winSC1ENCE/rancillio-mini/docs/img/trockenaufbau.png

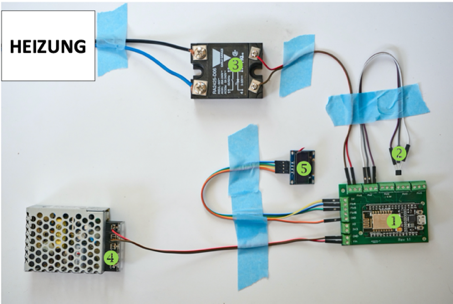
docs/img/trockenaufbau.png
