winSC1ENCE/rancillio-mini/docs/img/OnlyPIDRancilio.png

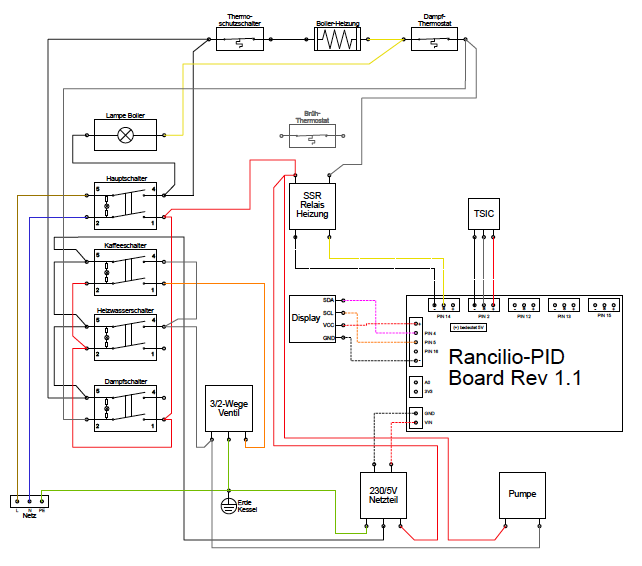
docs/img/OnlyPIDRancilio.png
