winSC1ENCE/rancillio-mini/docs/img/OrginalSchaltplanRancilio.png

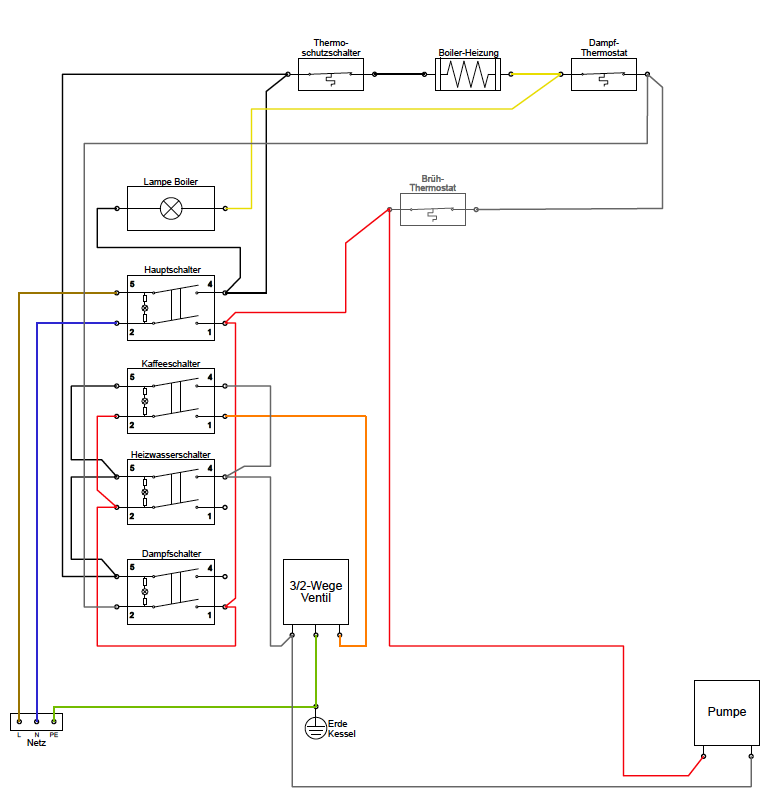
docs/img/OrginalSchaltplanRancilio.png
