winSC1ENCE/rancillio-mini/docs/img/platine_rev1.2.png

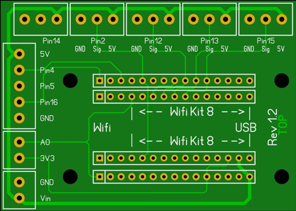
docs/img/platine_rev1.2.png
