winSC1ENCE/rancillio-mini/docs/img/relais_1.jpg

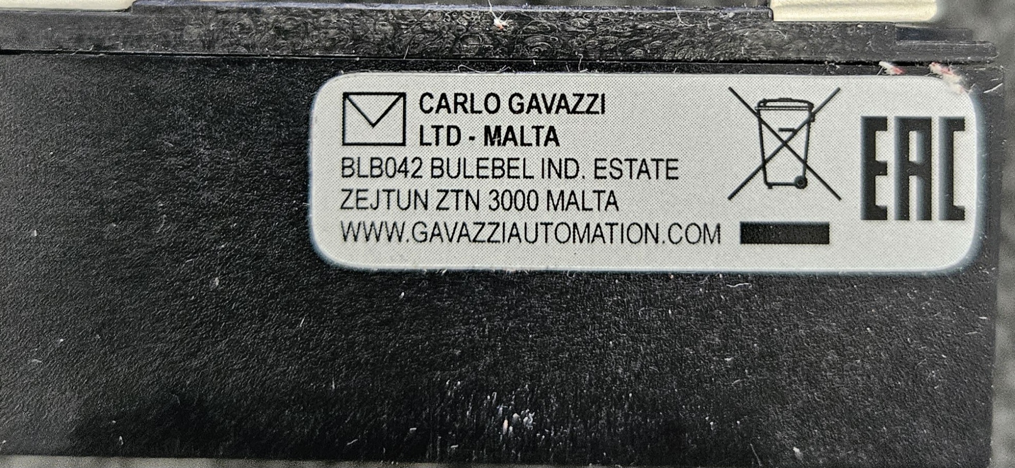
docs/img/relais_1.jpg
