winSC1ENCE/rancillio-mini/docs/img/relais_datasheet_1.jpg

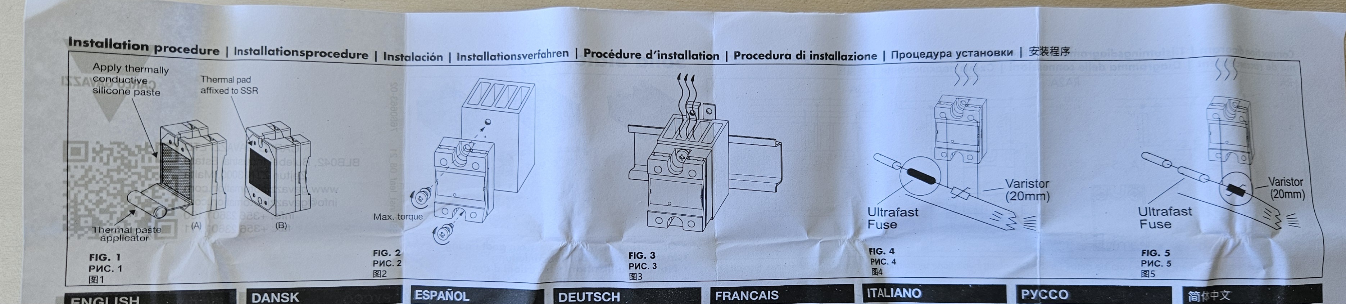
docs/img/relais_datasheet_1.jpg
