winSC1ENCE/rancillio-mini/docs/img/relais_datasheet_2.jpg

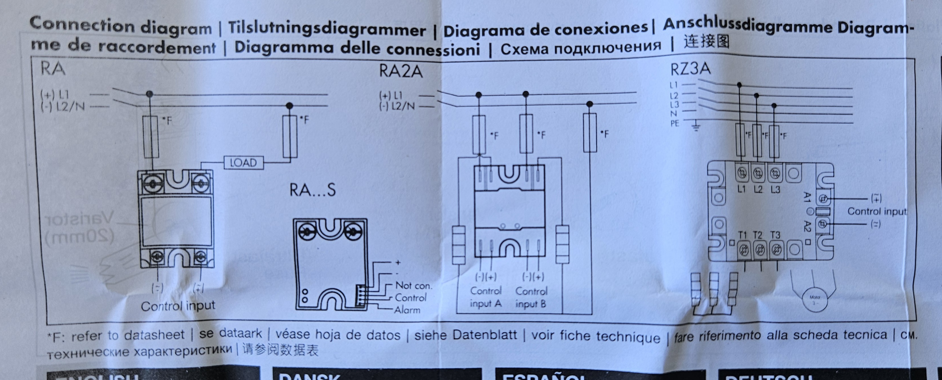
docs/img/relais_datasheet_2.jpg
