winSC1ENCE/rancillio-mini/docs/img/relais_datasheet_3.jpg

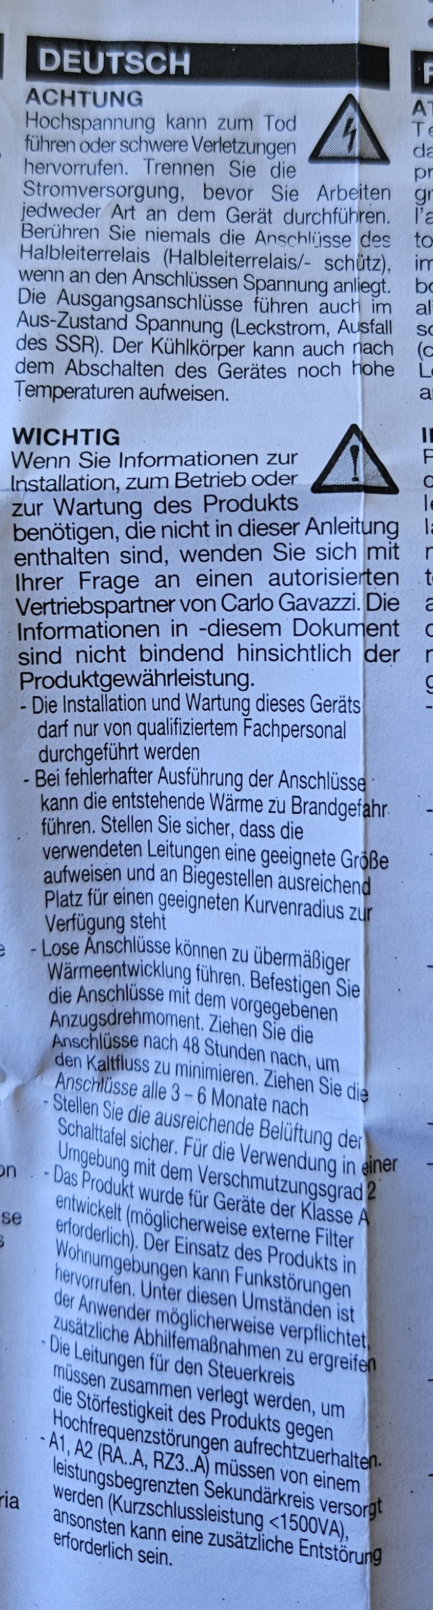
docs/img/relais_datasheet_3.jpg
