winSC1ENCE/rancillio-mini/docs/img/temp_sensor_belegung.jpg

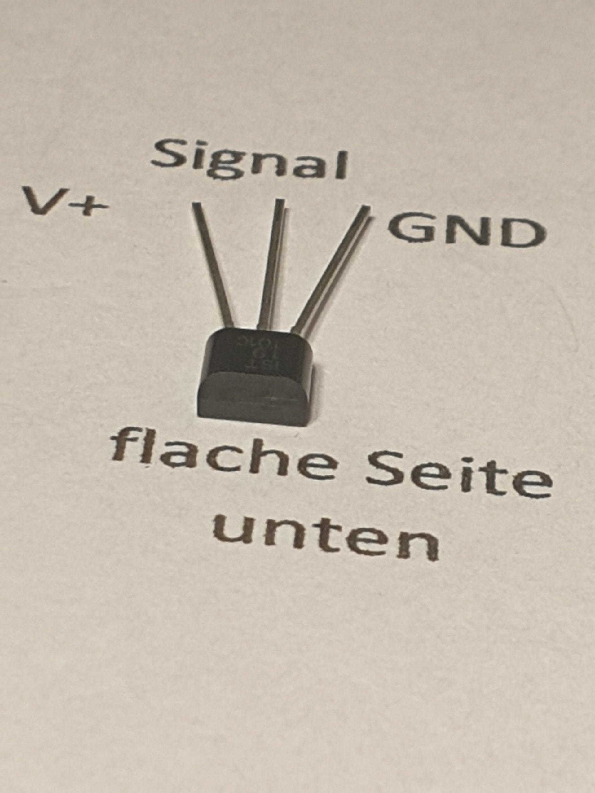
docs/img/temp_sensor_belegung.jpg
