winSC1ENCE/rancillio-mini/img/IMG_0040.jpeg

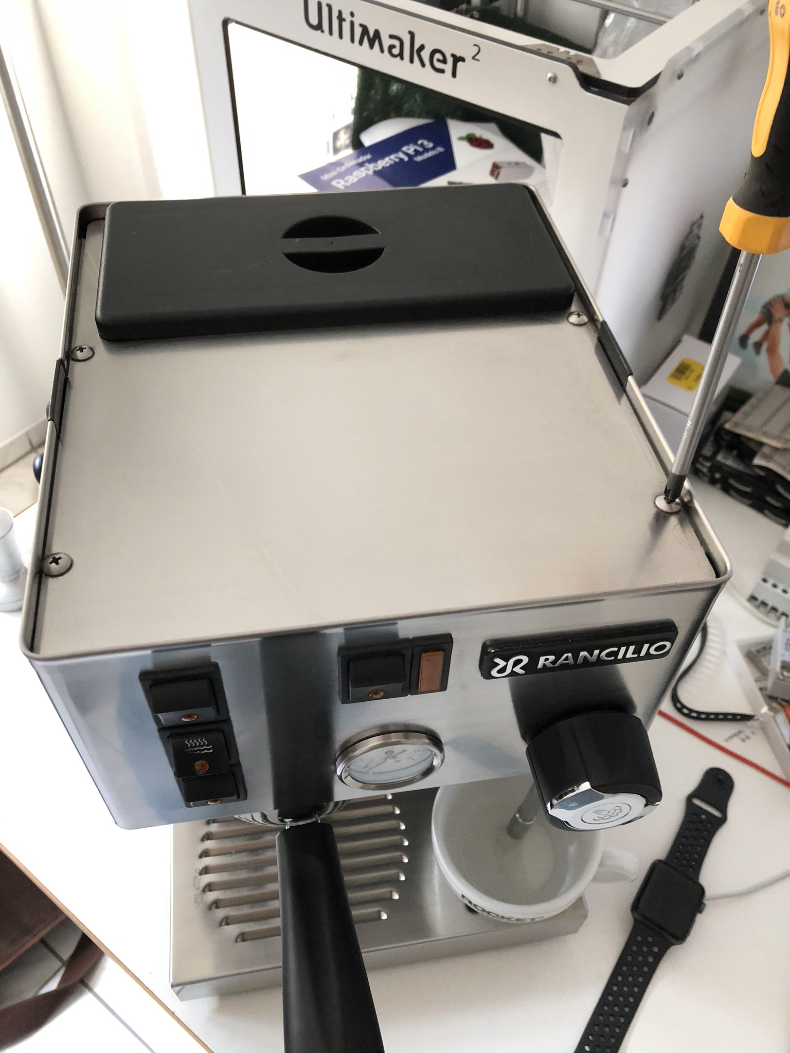
img/IMG_0040.jpeg
