winSC1ENCE/rancillio-mini/img/IMG_0041.jpeg

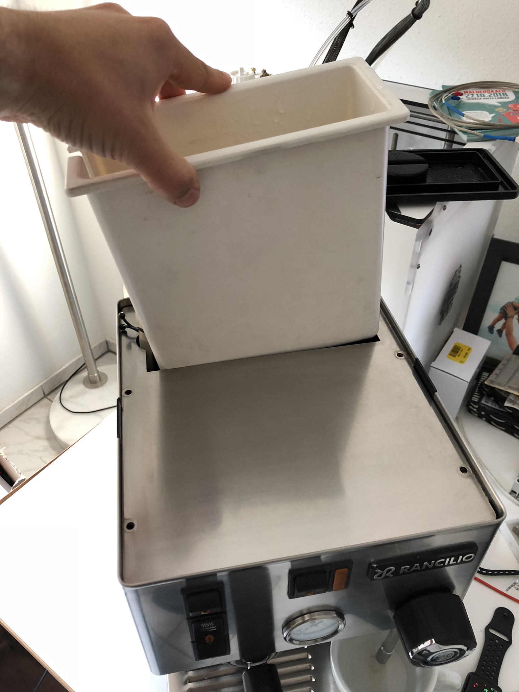
img/IMG_0041.jpeg
