winSC1ENCE/rancillio-mini/img/IMG_0042.jpeg

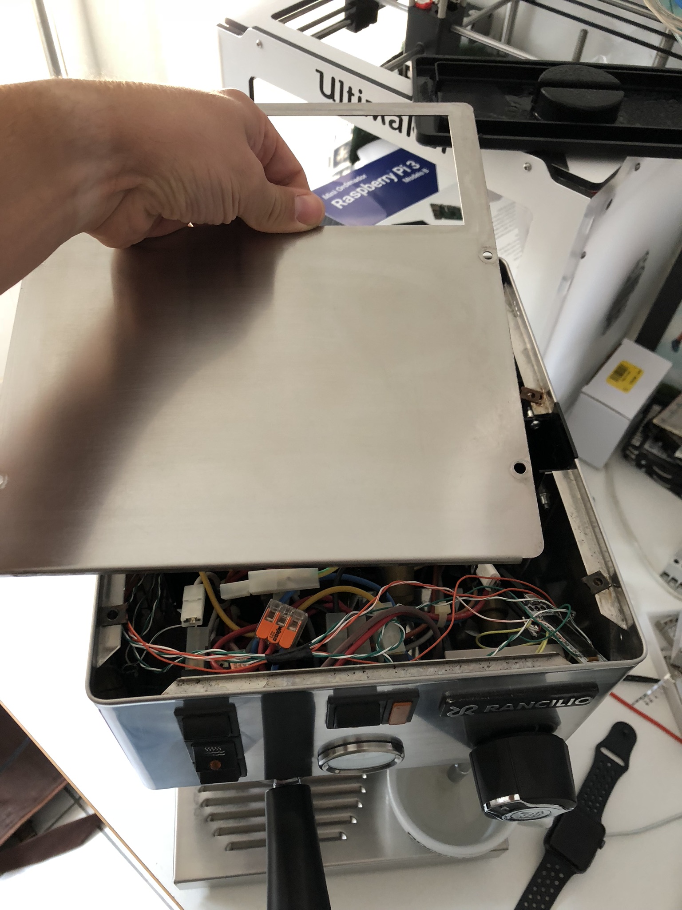
img/IMG_0042.jpeg
