winSC1ENCE/rancillio-mini/img/IMG_0043.jpeg

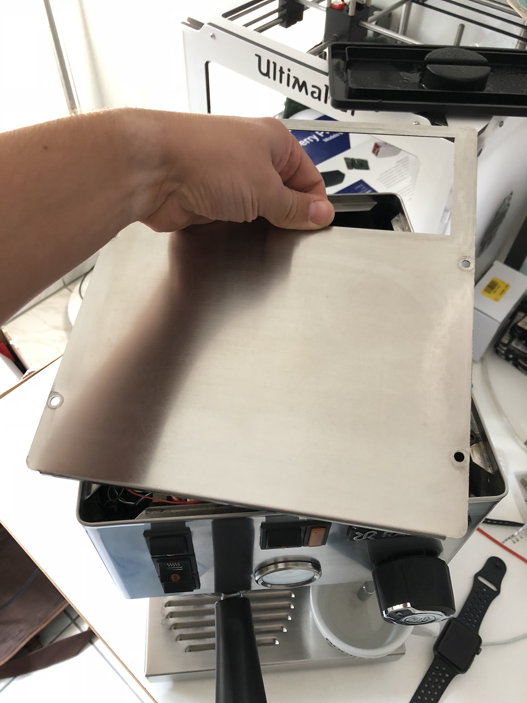
img/IMG_0043.jpeg
