winSC1ENCE/rancillio-mini/img/IMG_0044.jpeg

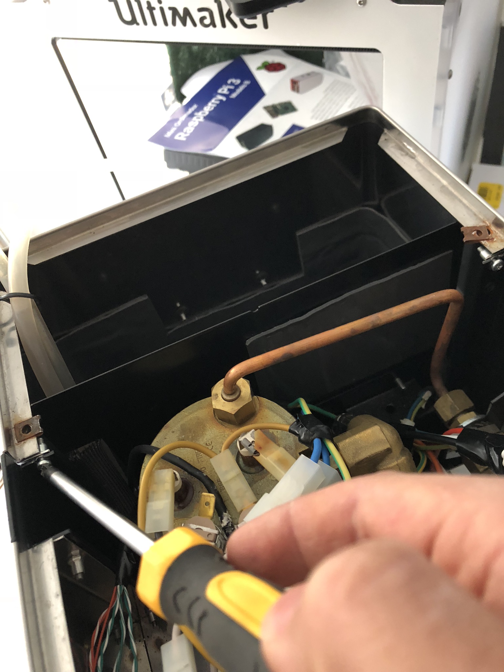
img/IMG_0044.jpeg
