winSC1ENCE/rancillio-mini/img/IMG_0045.jpeg

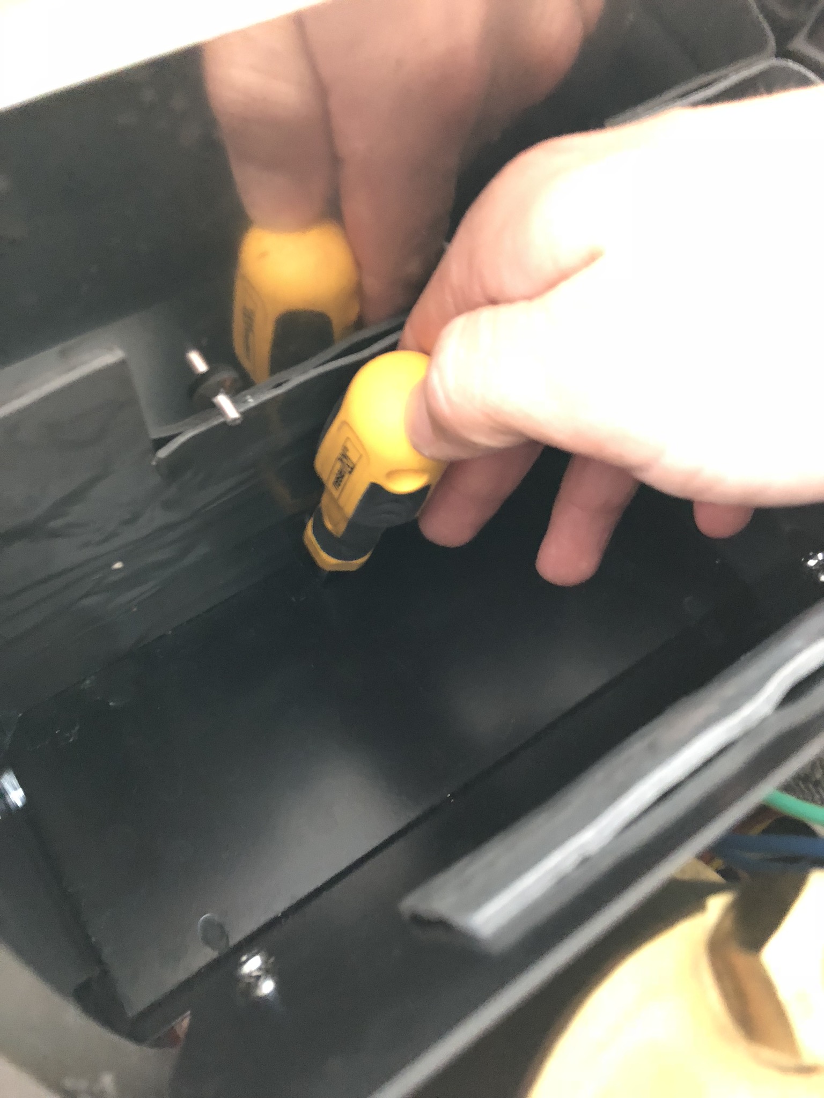
img/IMG_0045.jpeg
