winSC1ENCE/rancillio-mini/img/IMG_0046.jpeg

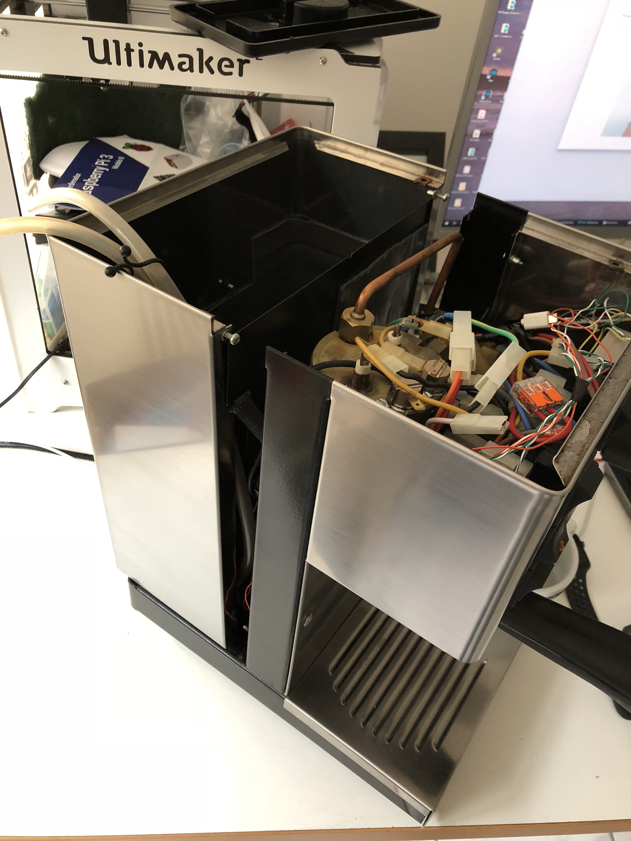
img/IMG_0046.jpeg
