winSC1ENCE/rancillio-mini/img/IMG_0047.jpeg

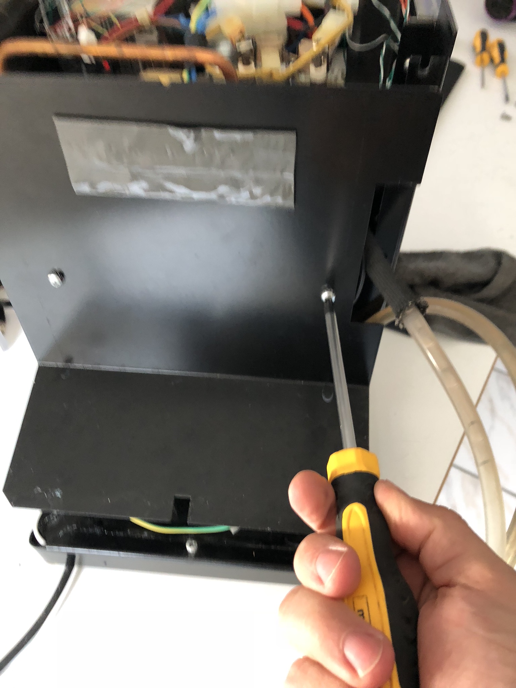
img/IMG_0047.jpeg
