winSC1ENCE/rancillio-mini/img/IMG_0048.jpeg

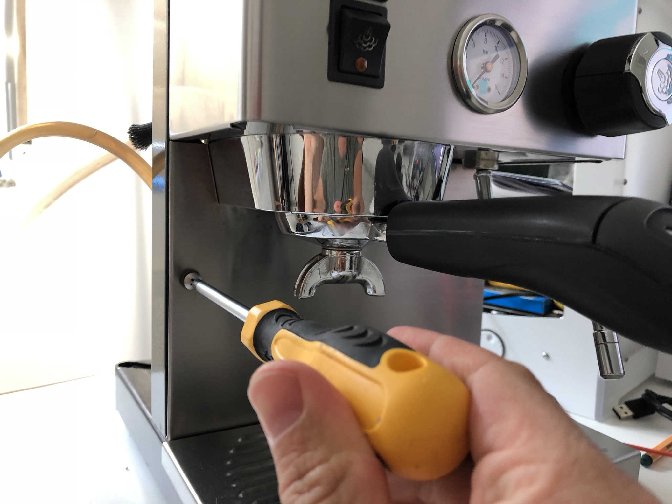
img/IMG_0048.jpeg
