winSC1ENCE/rancillio-mini/img/IMG_0049.jpeg

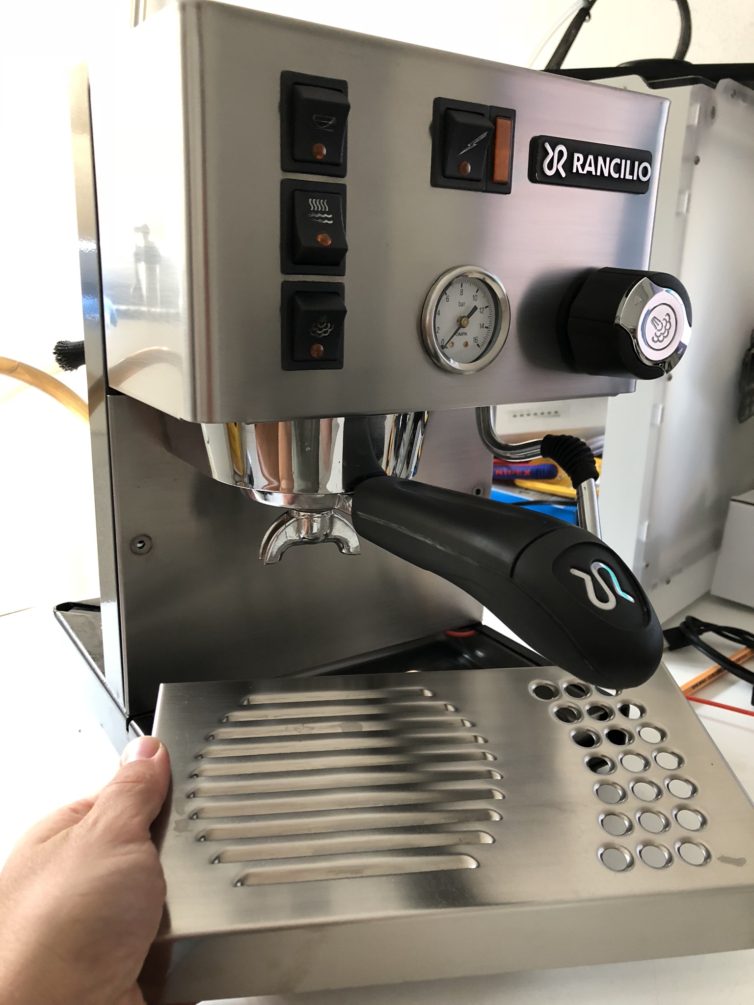
img/IMG_0049.jpeg
