winSC1ENCE/rancillio-mini/img/IMG_0050.jpeg

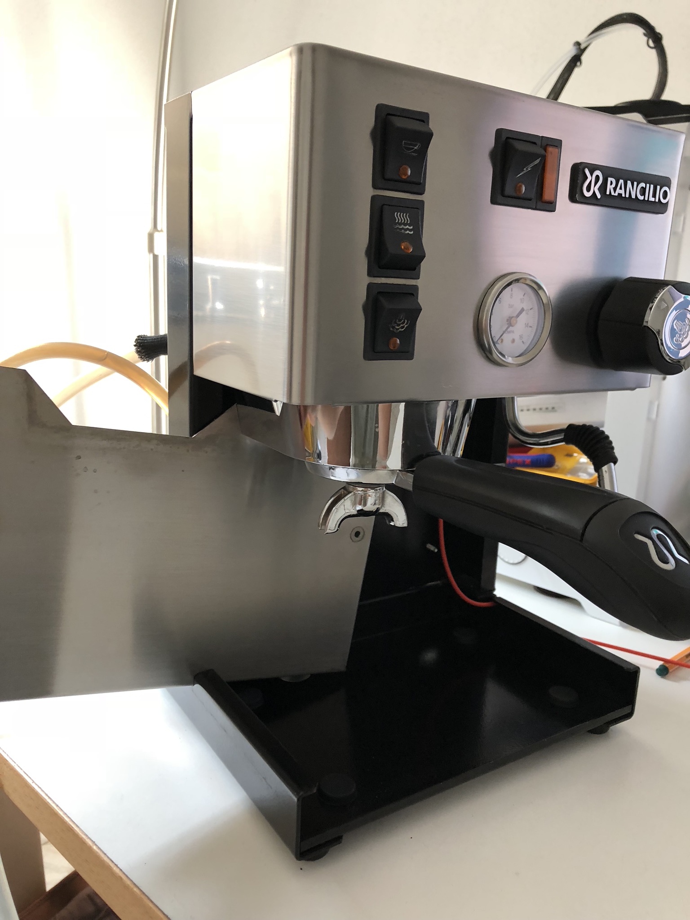
img/IMG_0050.jpeg
