winSC1ENCE/rancillio-mini/img/IMG_0076.jpeg

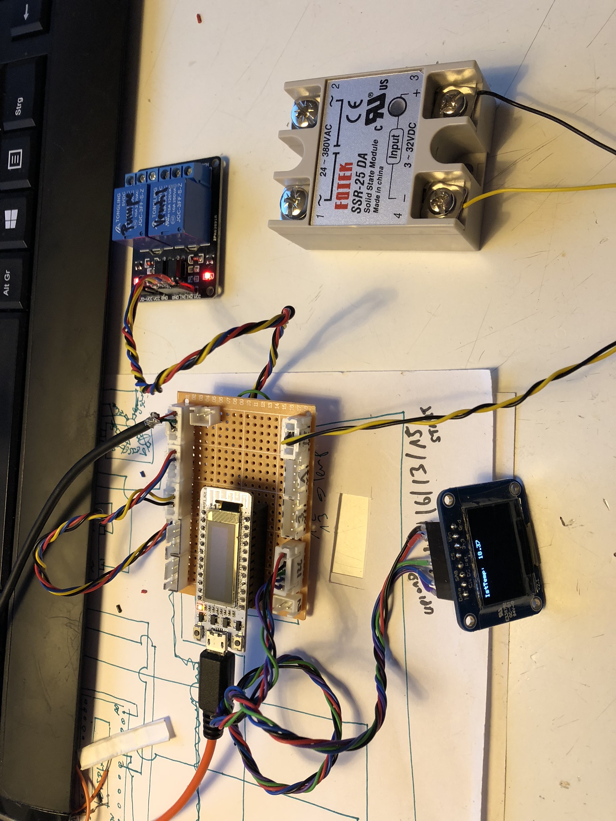
img/IMG_0076.jpeg
