winSC1ENCE/rancillio-mini/img/IMG_0078.jpeg

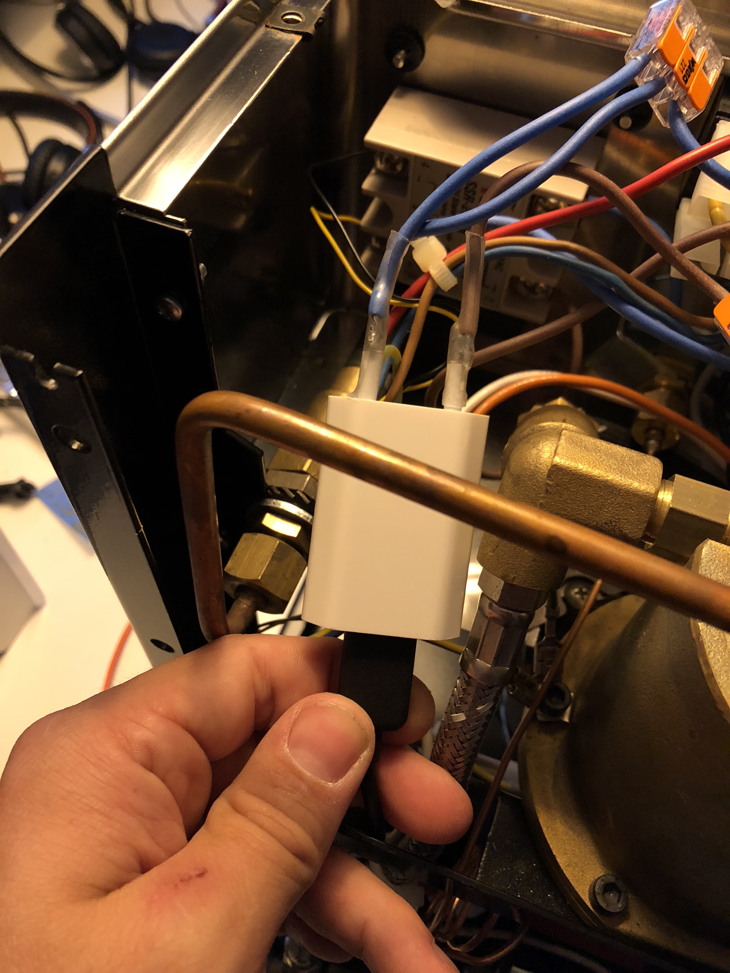
img/IMG_0078.jpeg
