winSC1ENCE/rancillio-mini/img/IMG_0079.jpeg

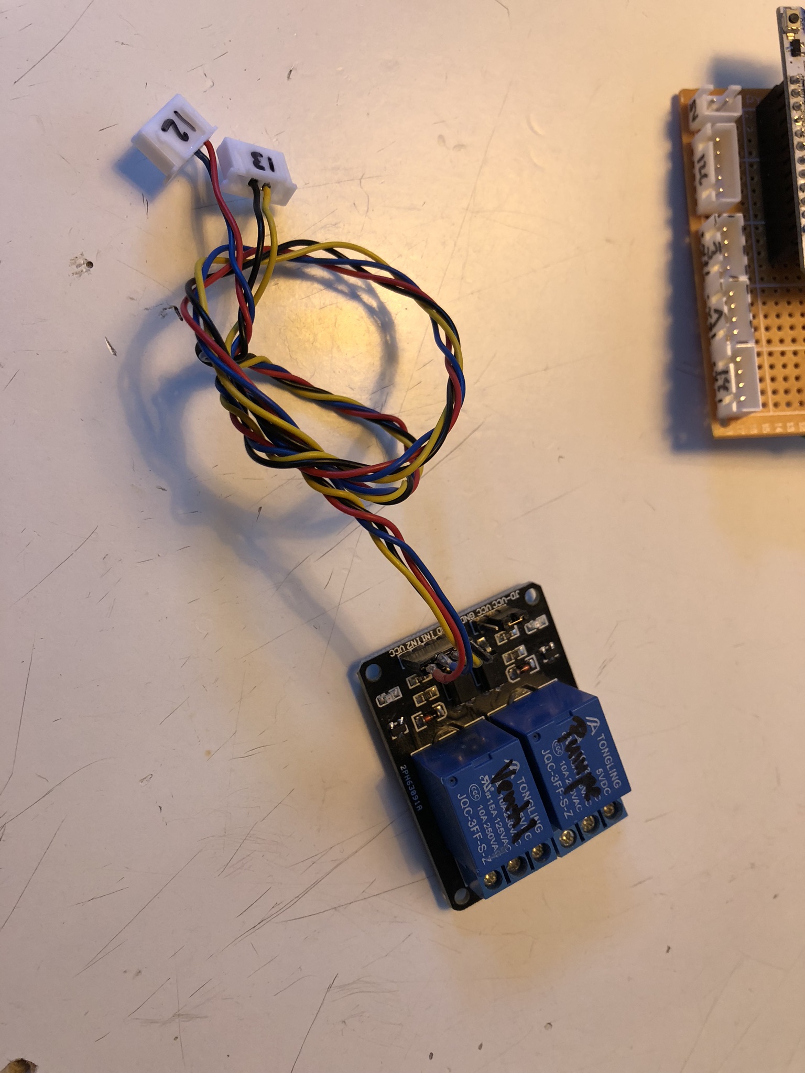
img/IMG_0079.jpeg
