winSC1ENCE/rancillio-mini/img/IMG_0080.jpeg

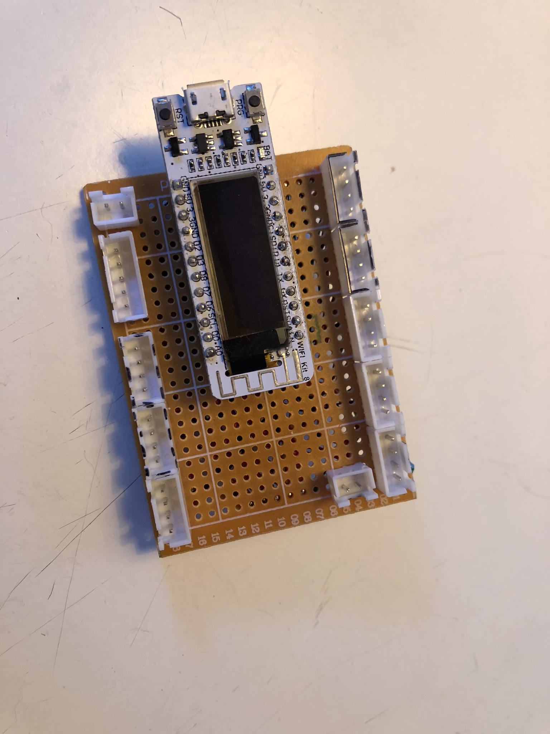
img/IMG_0080.jpeg
