winSC1ENCE/rancillio-mini/img/IMG_0081.jpeg

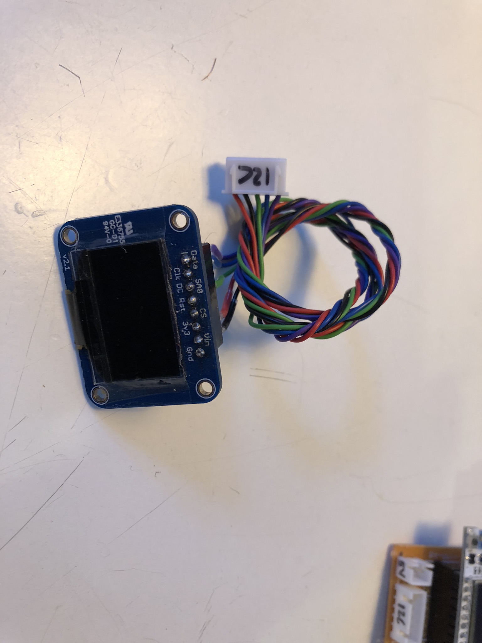
img/IMG_0081.jpeg
