winSC1ENCE/rancillio-mini/img/IMG_0082.jpeg

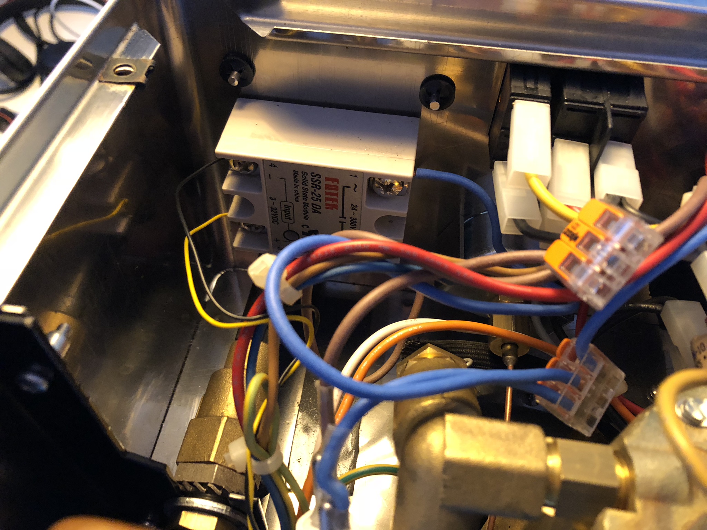
img/IMG_0082.jpeg
