winSC1ENCE/rancillio-mini/img/IMG_0083.jpeg

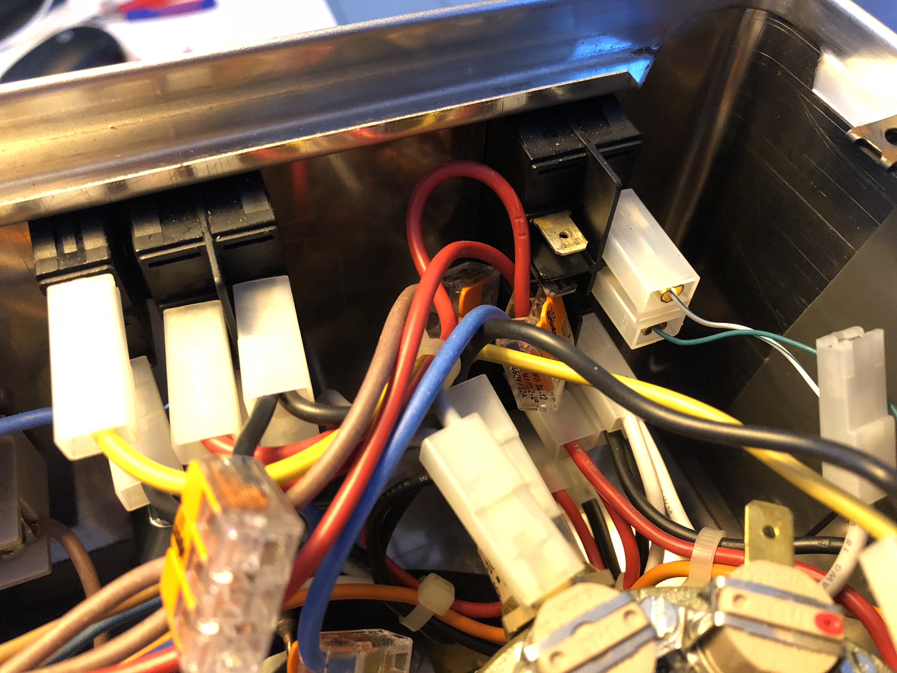
img/IMG_0083.jpeg
