winSC1ENCE/rancillio-mini/img/IMG_0084.jpeg

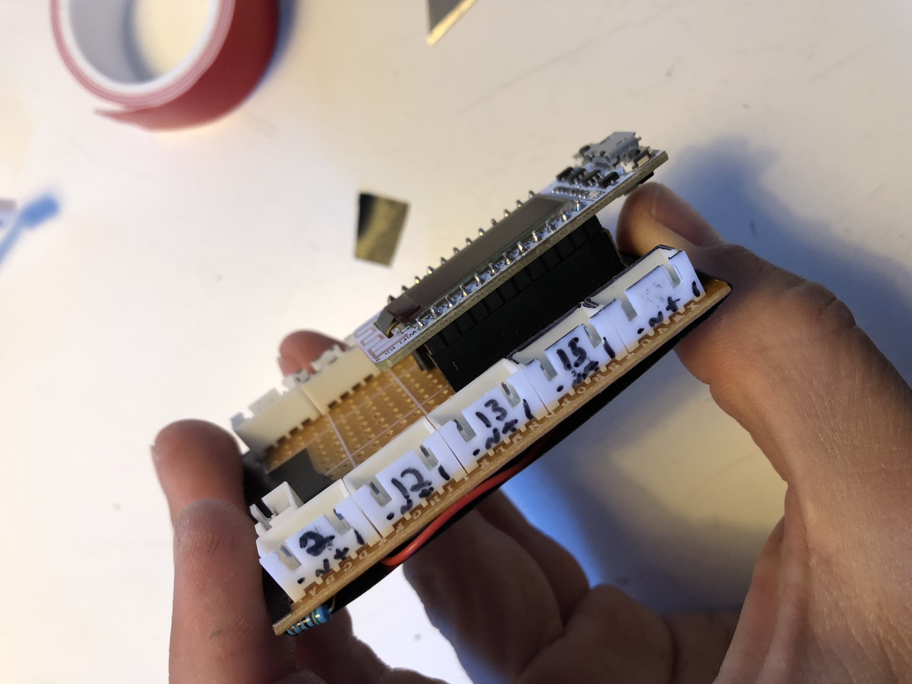
img/IMG_0084.jpeg
