winSC1ENCE/rancillio-mini/img/IMG_0085.jpeg

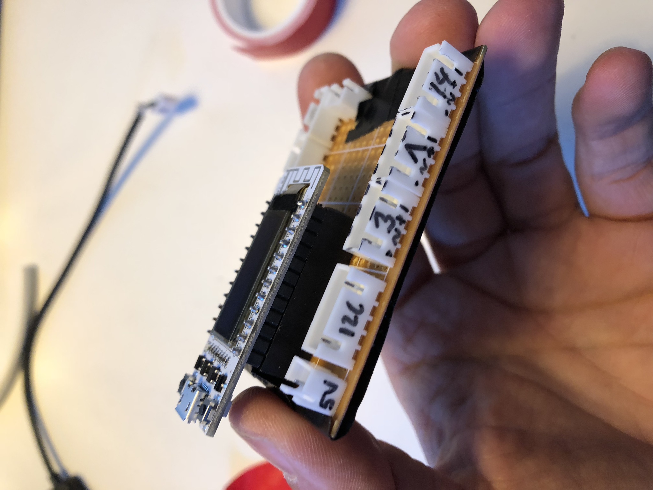
img/IMG_0085.jpeg
