winSC1ENCE/rancillio-mini/img/IMG_0086.jpeg

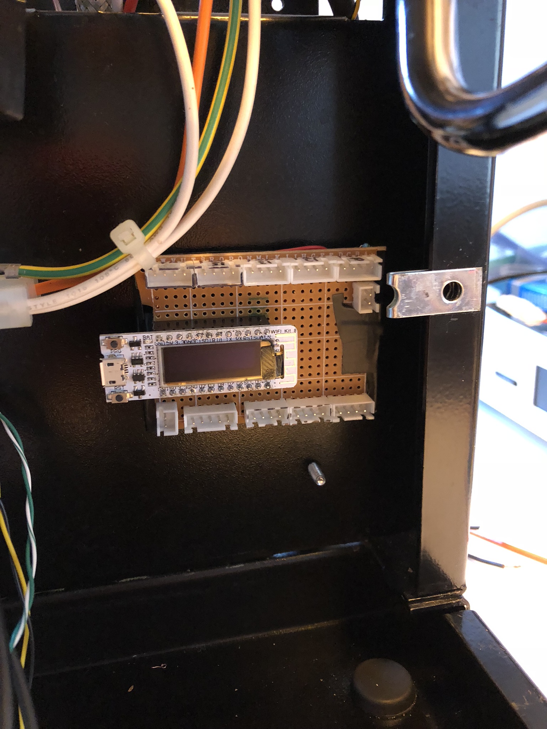
img/IMG_0086.jpeg
