winSC1ENCE/rancillio-mini/img/IMG_0087.jpeg

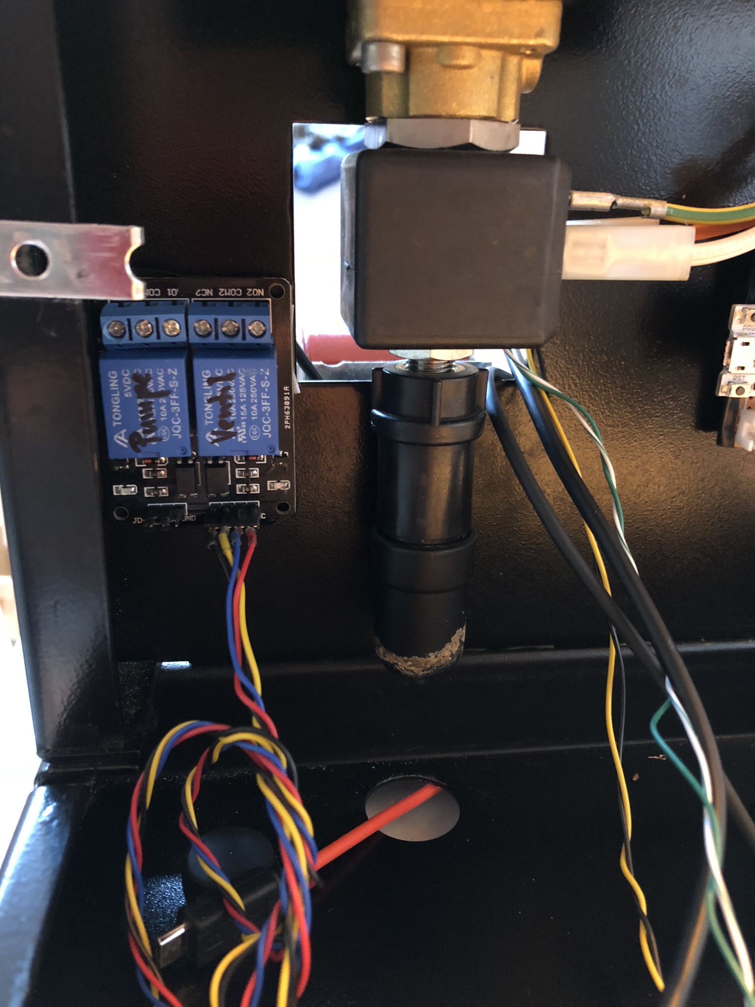
img/IMG_0087.jpeg
