winSC1ENCE/rancillio-mini/img/IMG_0088.jpeg

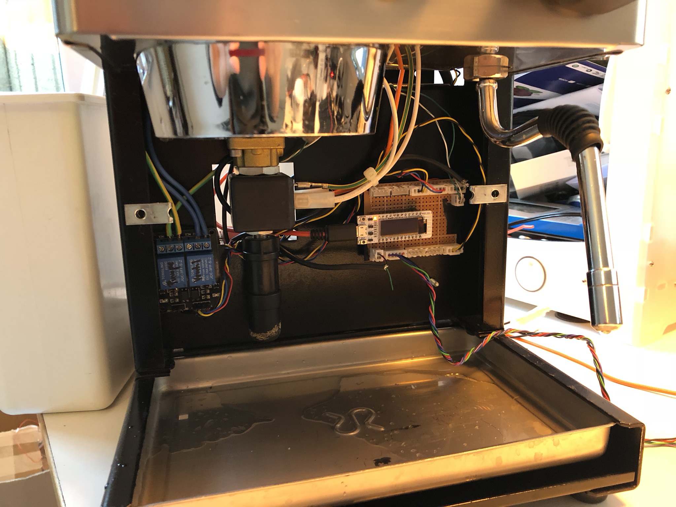
img/IMG_0088.jpeg
