winSC1ENCE/rancillio-mini/img/IMG_0090.jpeg

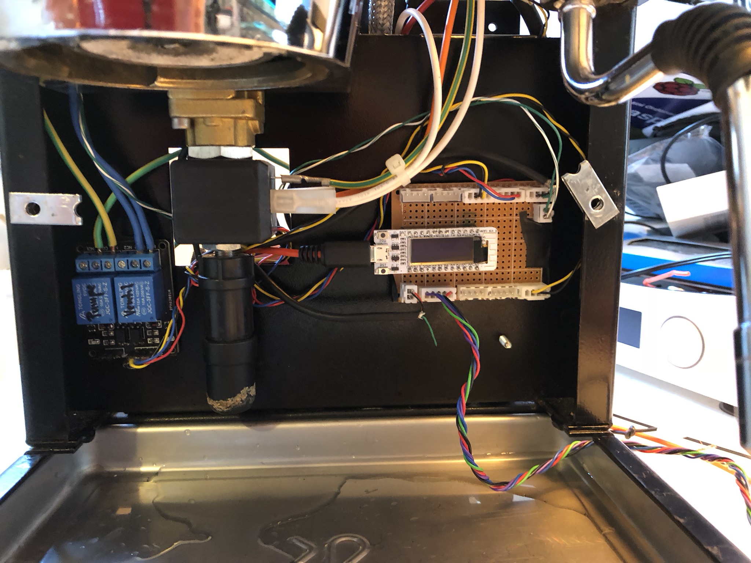
img/IMG_0090.jpeg
