winSC1ENCE/rancillio-mini/img/IMG_0091.jpeg

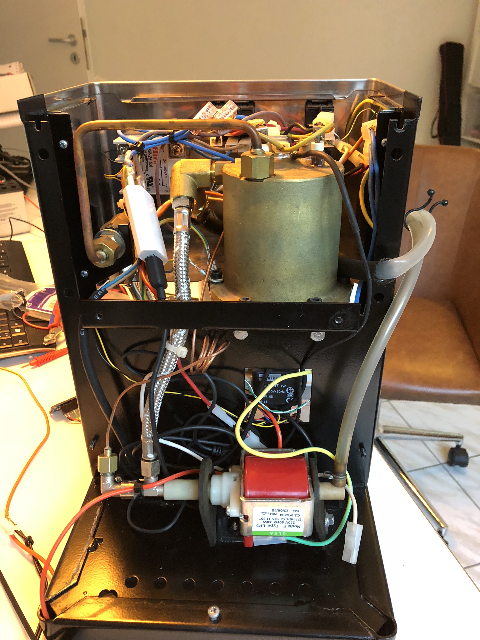
img/IMG_0091.jpeg
