winSC1ENCE/rancillio-mini/img/IMG_0092.jpeg

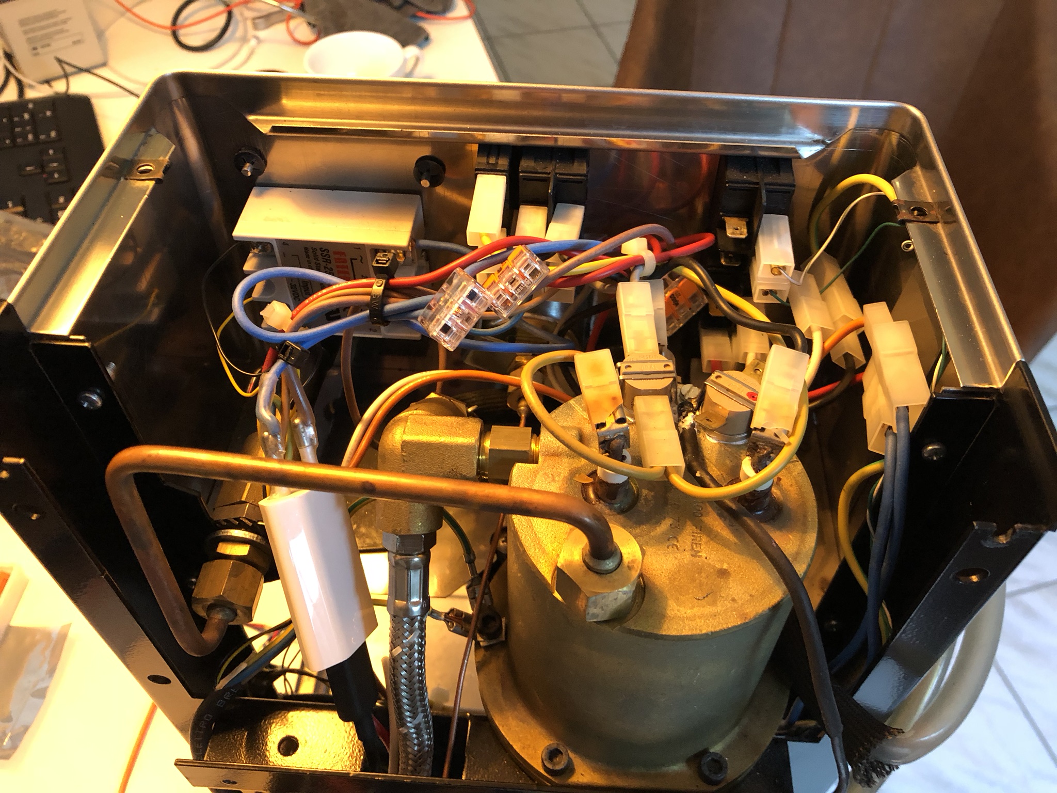
img/IMG_0092.jpeg
