winSC1ENCE/rancillio-mini/img/IMG_0097.jpeg

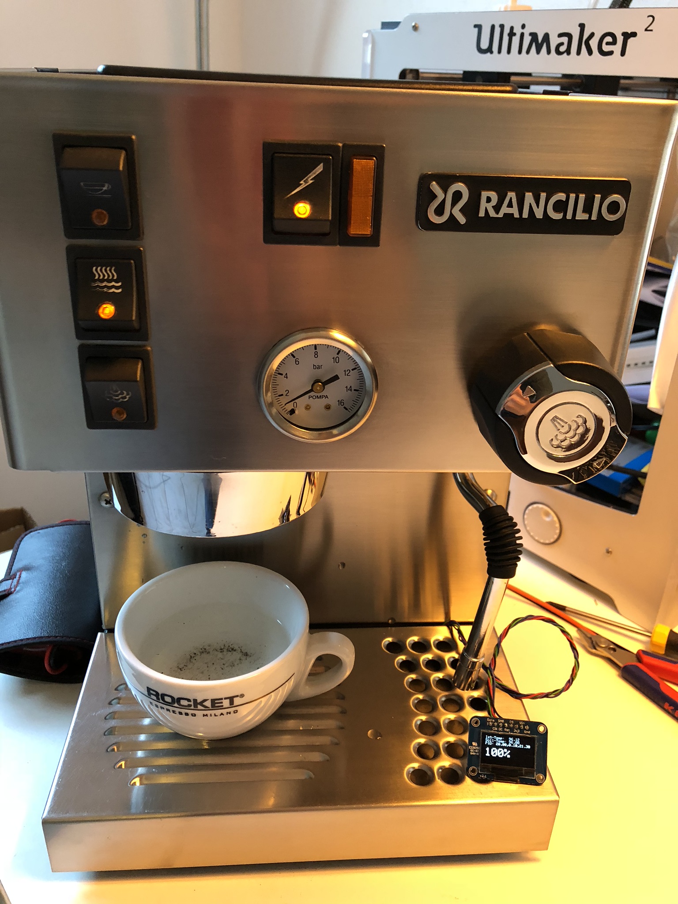
img/IMG_0097.jpeg
