winSC1ENCE/rancillio-mini/img/IMG_0099.jpeg

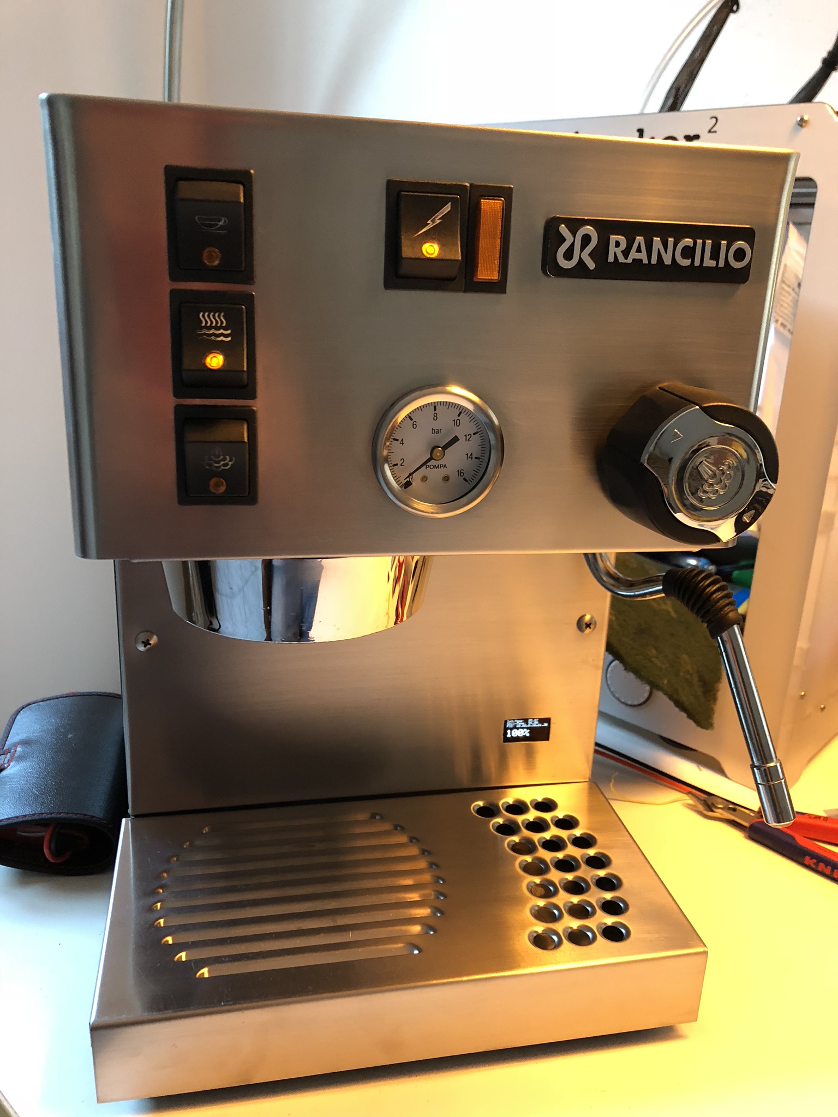
img/IMG_0099.jpeg
