winSC1ENCE/rancillio-mini/img/IMG_0100.jpeg

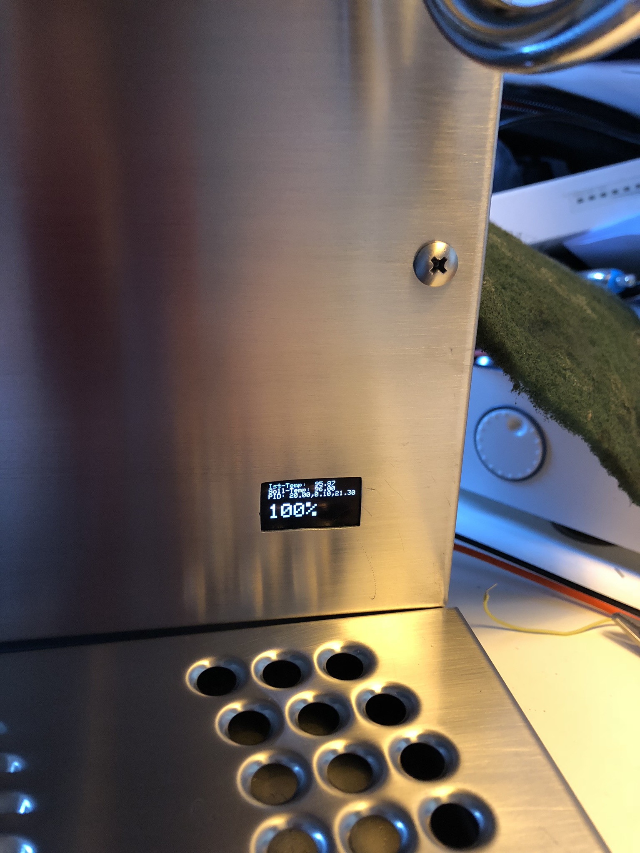
img/IMG_0100.jpeg
