winSC1ENCE/rancillio-mini/img/Rancilio-Cable-Full.jpg

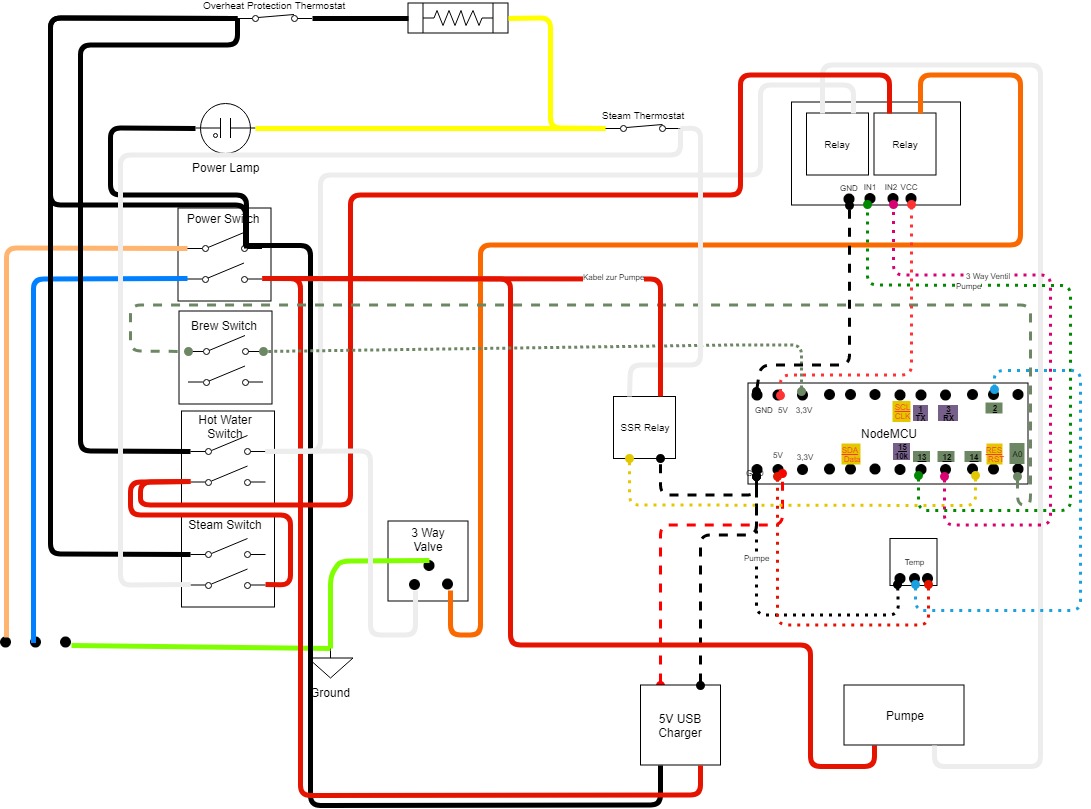
img/Rancilio-Cable-Full.jpg
