winSC1ENCE/rancillio-mini/img/Rancilio-Cable-Only PID.jpg

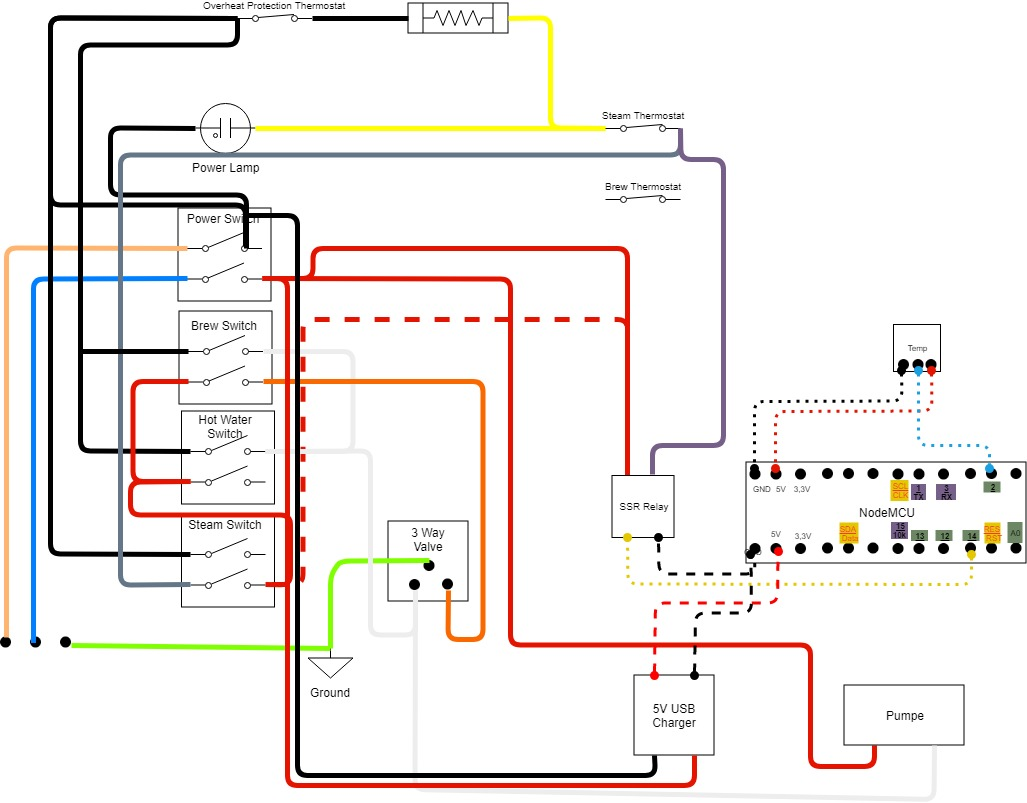
img/Rancilio-Cable-Only PID.jpg
