winSC1ENCE/rancillio-mini/img/Rancilio-Cable-Original.jpg

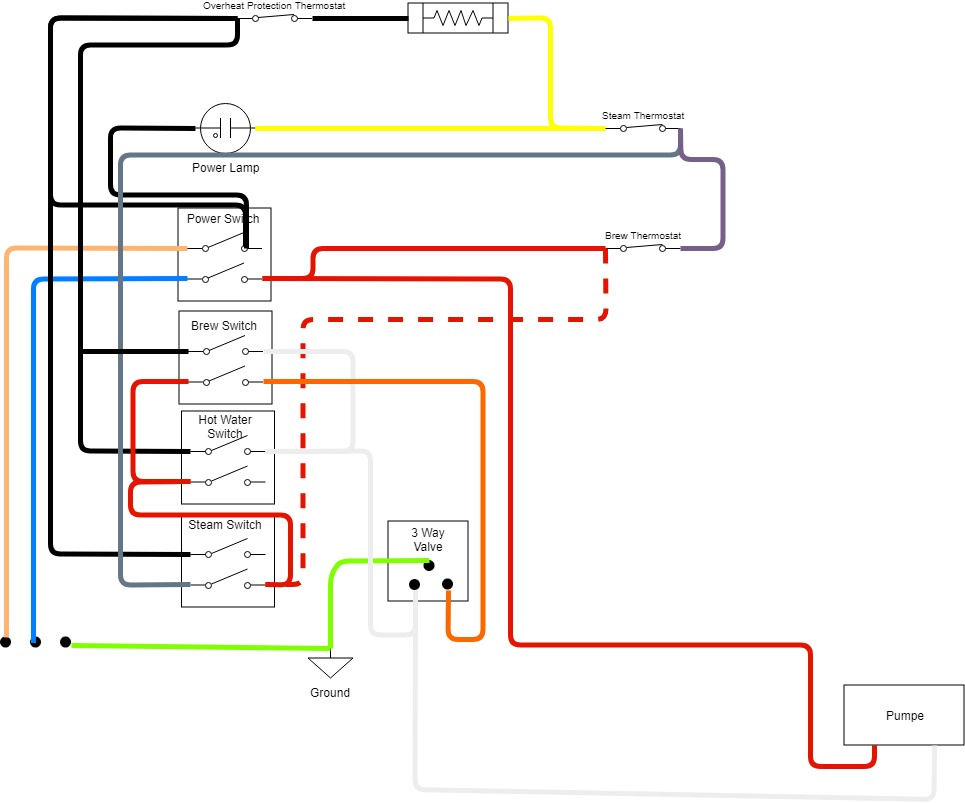
img/Rancilio-Cable-Original.jpg
