winSC1ENCE/rancillio-mini/img/Rancilio-Cable-Page-4.jpg

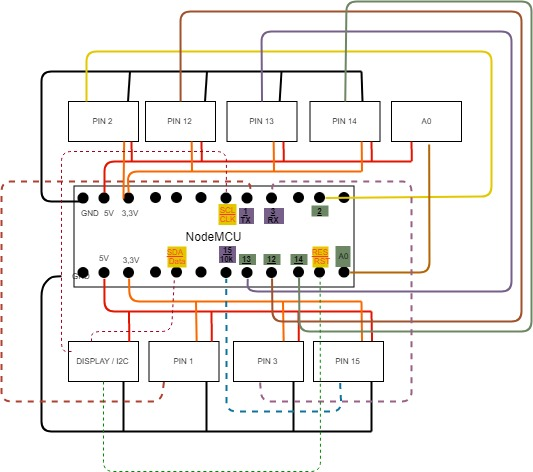
img/Rancilio-Cable-Page-4.jpg
