winSC1ENCE/rancillio-mini/docs/img/netzteil.jpg

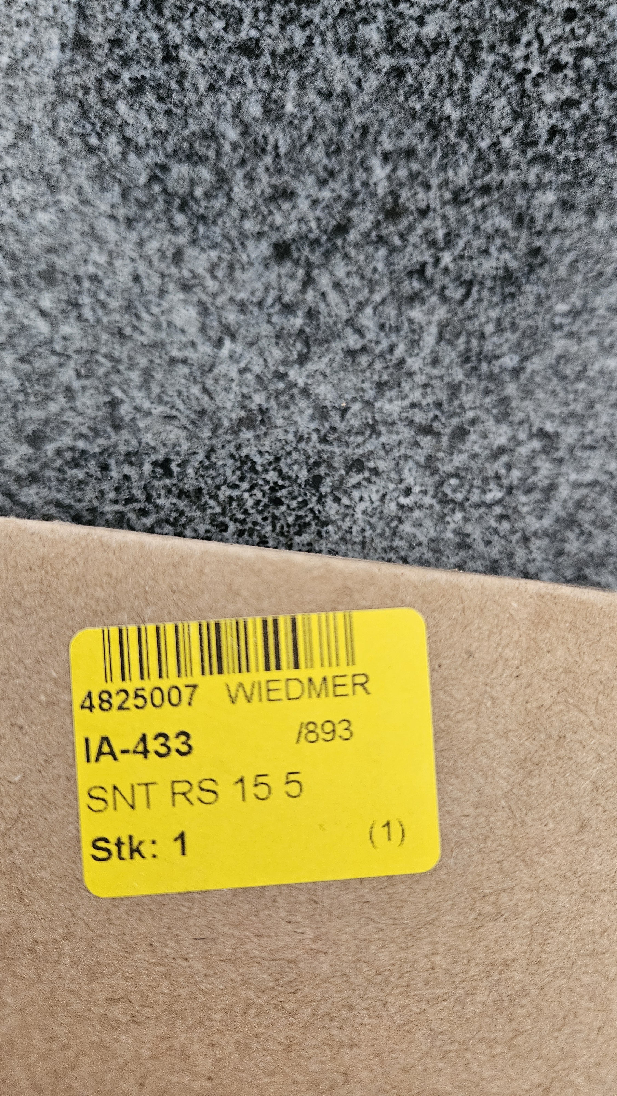
docs/img/netzteil.jpg
